SeeedDocument/Seeed_IoTea/seeedtea/CO2.h

// CO2.h

#ifndef _CO2_h
#define _CO2_h

#if defined(ARDUINO) && ARDUINO >= 100
	#include "arduino.h"
#else
	#include "WProgram.h"
#endif
extern void CO2_init(void);
extern unsigned int CO2_dataRecieve(void);
extern void Feed_dog(void);		//喂狗，同时闪灯

#endif
