SeeedDocument/Seeed_IoTea/seeedtea/Dust_other.h

// Dust_other.h

#ifndef _DUST_OTHER_h
#define _DUST_OTHER_h

#if defined(ARDUINO) && ARDUINO >= 100
	#include "arduino.h"
#else
	#include "WProgram.h"
#endif
//extern const int Dust_pin;
#define Dust_pin 3
extern float Dust_concentration(void);
extern int O2_value(void);
extern void Feed_dog(void);		//喂狗，同时闪灯


#endif
